Kirill-DoS/wasserschwein/hardware/cad/back_form_pusher.FCStd

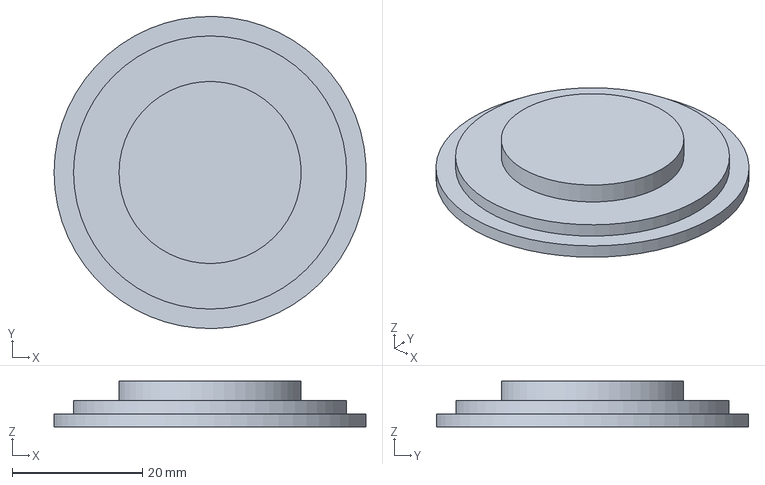
[picture p15: CAD file, 2026-05-06]
hardware/cad/back_form_pusher.FCStd
48.0 x 48.0 x 7.00 mm
