Kirill-DoS/wasserschwein/hardware/cad/NewPusherSys/ArmTightening.FCStd

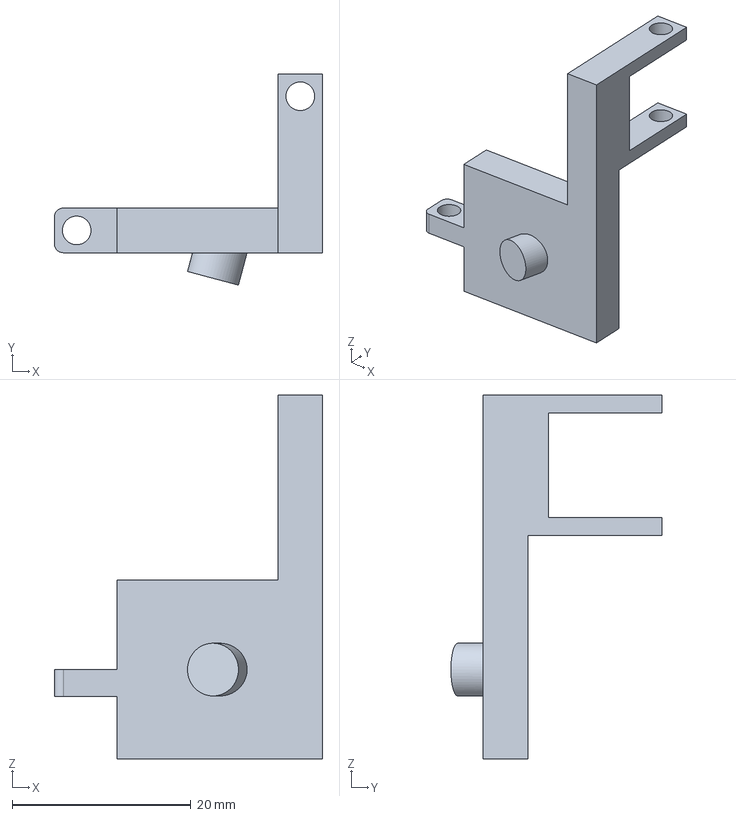
[picture p16: CAD file, 2026-05-06]
hardware/cad/NewPusherSys/ArmTightening.FCStd
30.0 x 23.6 x 40.7 mm
