Kirill-DoS/wasserschwein/hardware/cad/form_pusher.FCStd

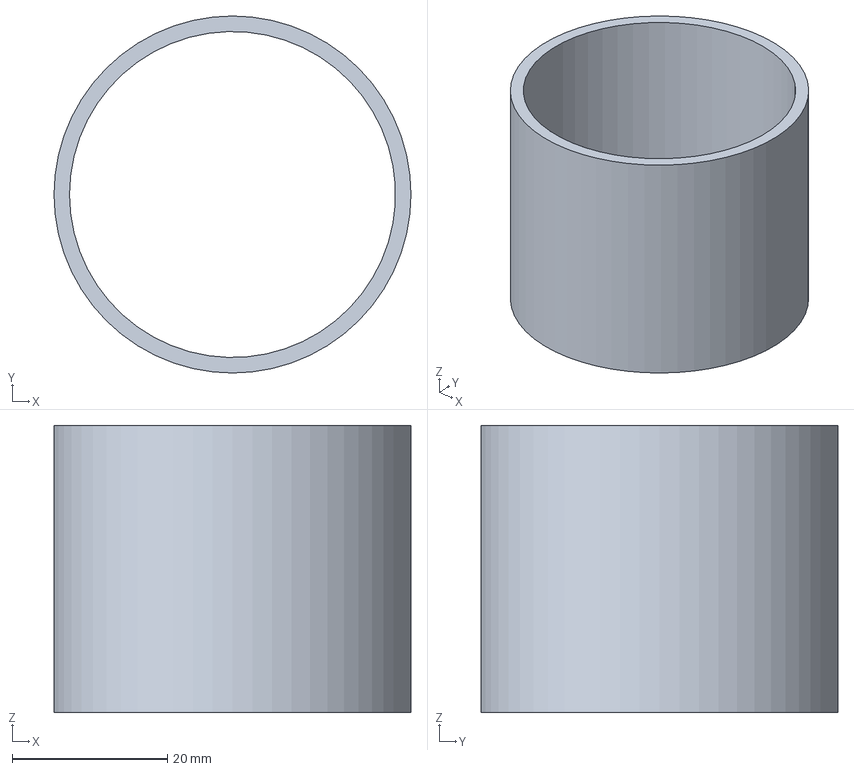
[picture p17: CAD file, 2026-05-06]
hardware/cad/form_pusher.FCStd
46.0 x 46.0 x 37.0 mm
