Kirill-DoS/wasserschwein/hardware/cad/NewPusherSys/BigGear.FCStd

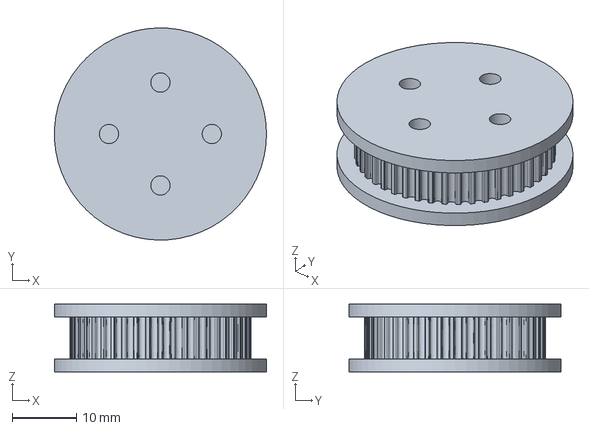
[picture p18: CAD file, 2026-05-06]
hardware/cad/NewPusherSys/BigGear.FCStd
33.0 x 33.0 x 10.5 mm
