Kirill-DoS/wasserschwein/hardware/cad/curtainDrive.FCStd

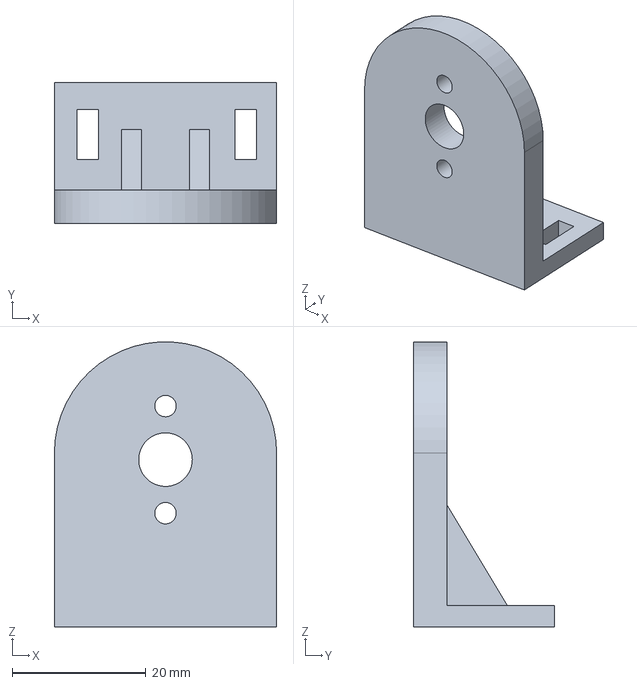
[picture p19: CAD file, 2026-05-06]
hardware/cad/curtainDrive.FCStd
33.2 x 21.0 x 42.6 mm
