Kirill-DoS/wasserschwein/hardware/cad/NewPusherSys/CurtainDrive.FCStd

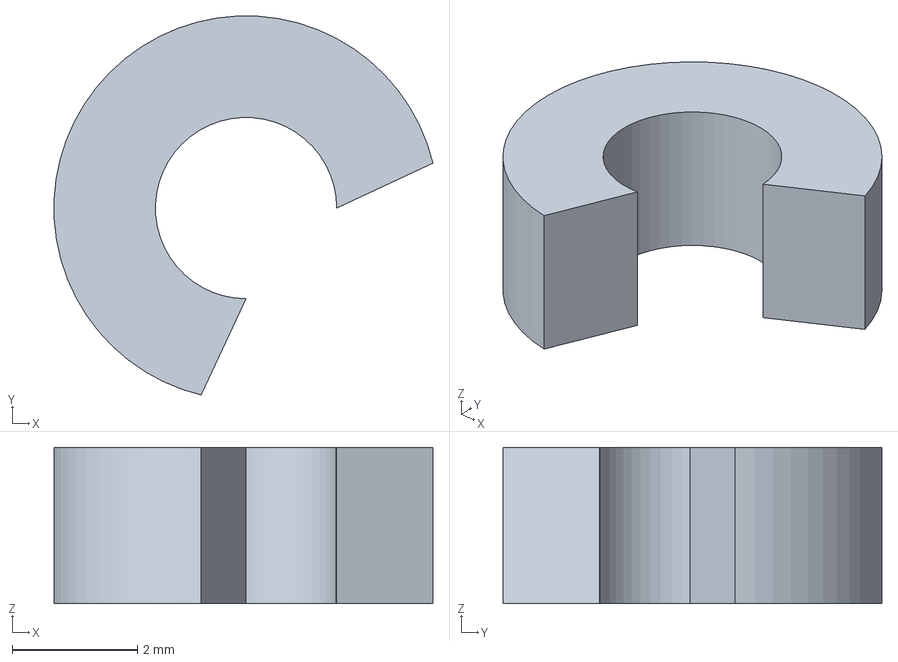
[picture p20: CAD file, 2026-05-06]
hardware/cad/NewPusherSys/CurtainDrive.FCStd
6.06 x 6.06 x 2.50 mm
