Kirill-DoS/wasserschwein/hardware/cad/NewPusherSys/WeelTightening.FCStd

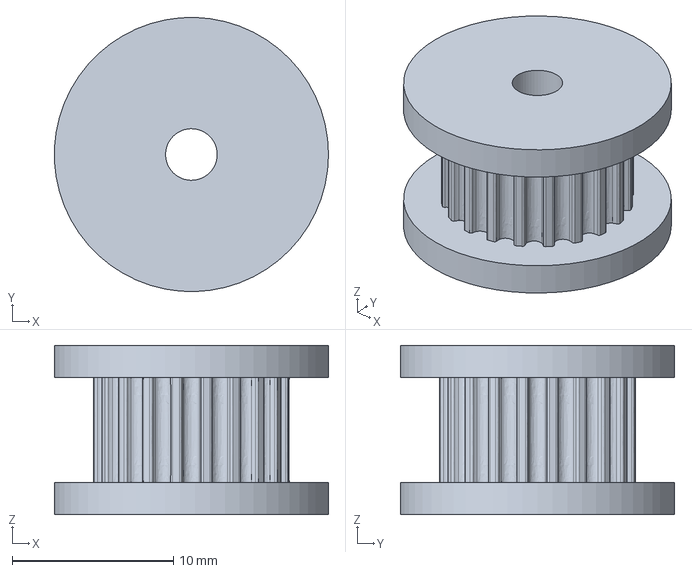
[picture p21: CAD file, 2026-05-06]
hardware/cad/NewPusherSys/WeelTightening.FCStd
17.0 x 17.0 x 10.5 mm
