Kirill-DoS/wasserschwein/hardware/cad/weel_involute_gear.FCStd

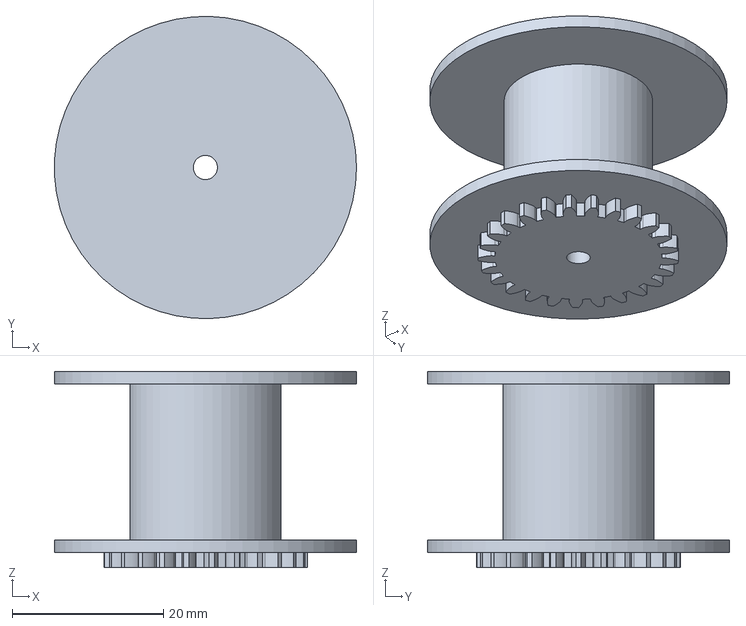
[picture p22: CAD file, 2026-03-06]
hardware/cad/weel_involute_gear.FCStd
40.0 x 40.0 x 26.0 mm
