Kirill-DoS/wasserschwein/hardware/cad/bevel_gear_3.FCStd

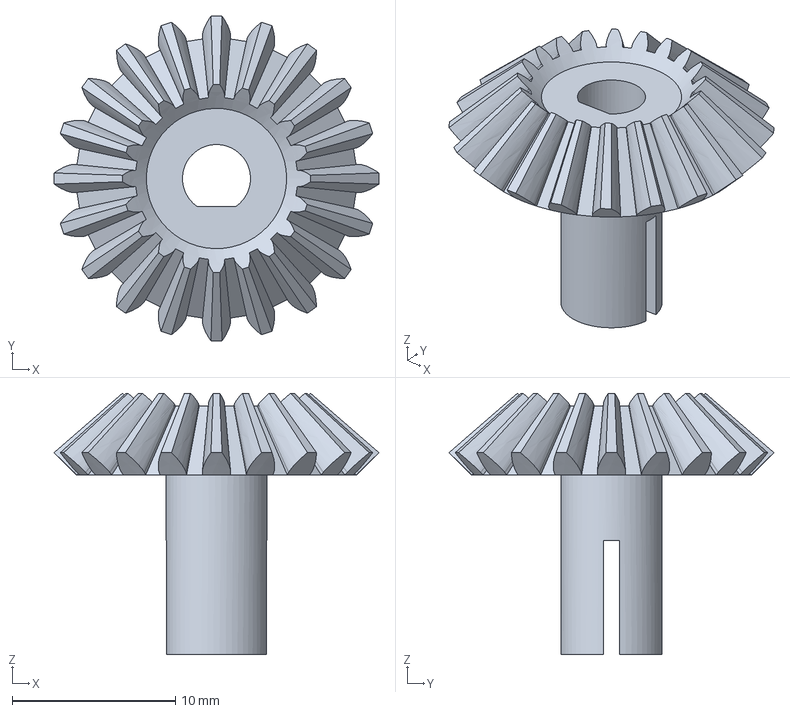
[picture p23: CAD file, 2026-03-06]
hardware/cad/bevel_gear_3.FCStd
19.9 x 19.9 x 16.0 mm
