Kirill-DoS/wasserschwein/hardware/cad/BLCD_kipper.FCStd

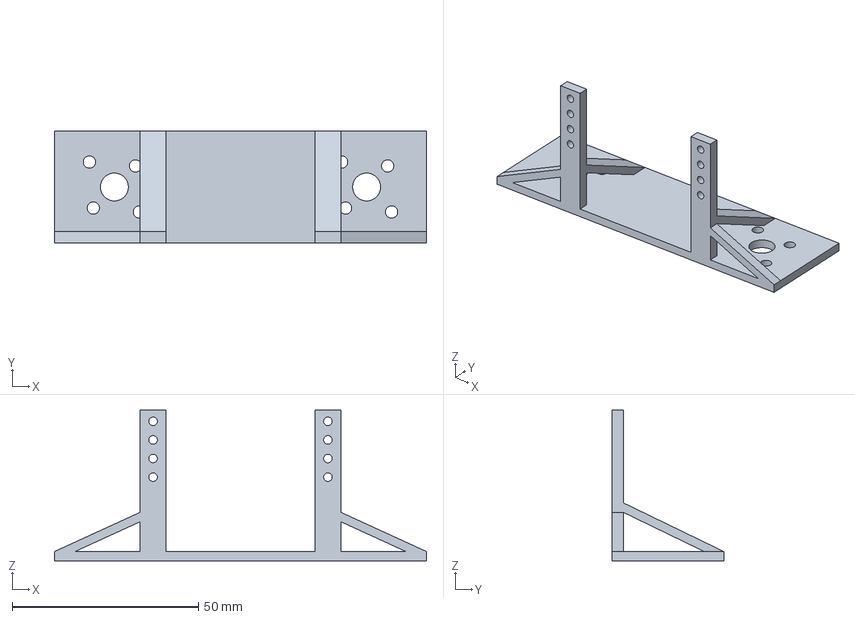
[picture p24: CAD file, 2026-03-06]
hardware/cad/BLCD_kipper.FCStd
100.0 x 30.0 x 40.5 mm
