Kirill-DoS/wasserschwein/hardware/cad/arcanoid_new.FCStd

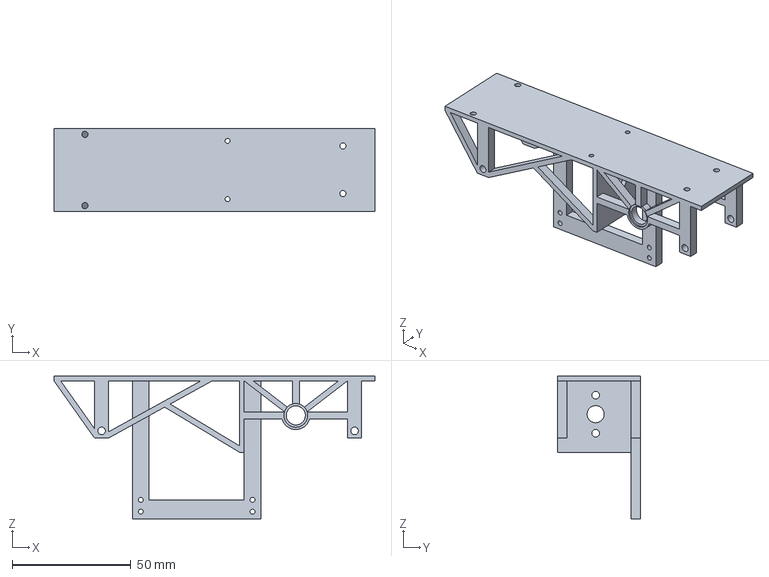
[picture p25: CAD file, 2026-03-06]
hardware/cad/arcanoid_new.FCStd
135.0 x 34.8 x 60.0 mm
