Kirill-DoS/wasserschwein/hardware/cad/brain_kipper.FCStd

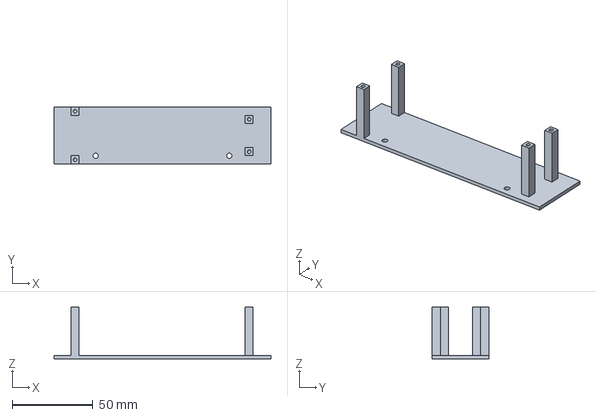
[picture p26: CAD file, 2026-03-06]
hardware/cad/brain_kipper.FCStd
134.0 x 35.0 x 32.0 mm
