Kirill-DoS/wasserschwein/hardware/cad/board_stands.3mf

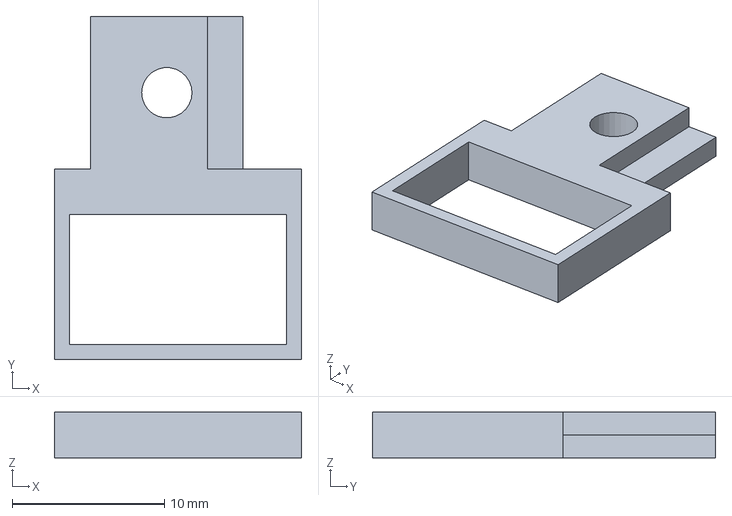
[picture p27: CAD file, 2026-03-06]
hardware/cad/board_stands.3mf
16.2 x 22.5 x 3.00 mm
