Kirill-DoS/wasserschwein/hardware/cad/lateral_weel.FCStd

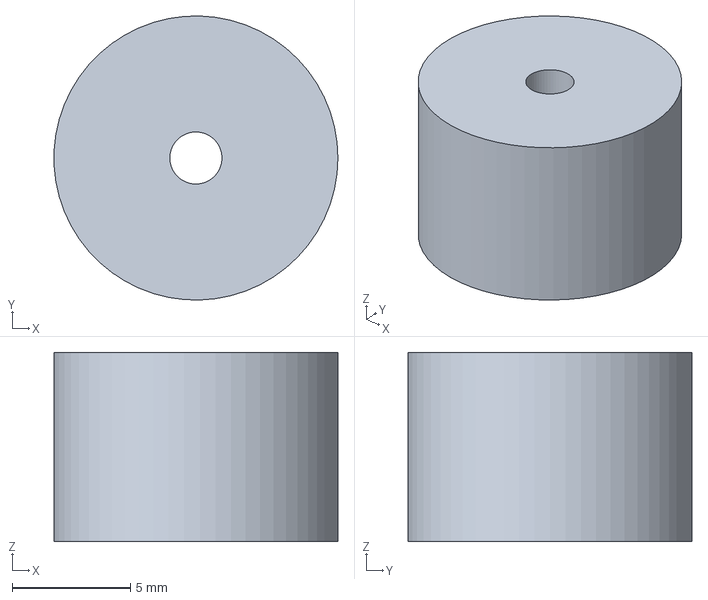
[picture p28: CAD file, 2026-01-27]
hardware/cad/lateral_weel.FCStd
12.0 x 12.0 x 8.00 mm
