Kirill-DoS/wasserschwein/hardware/cad/arcanoid1.3mf.FCStd

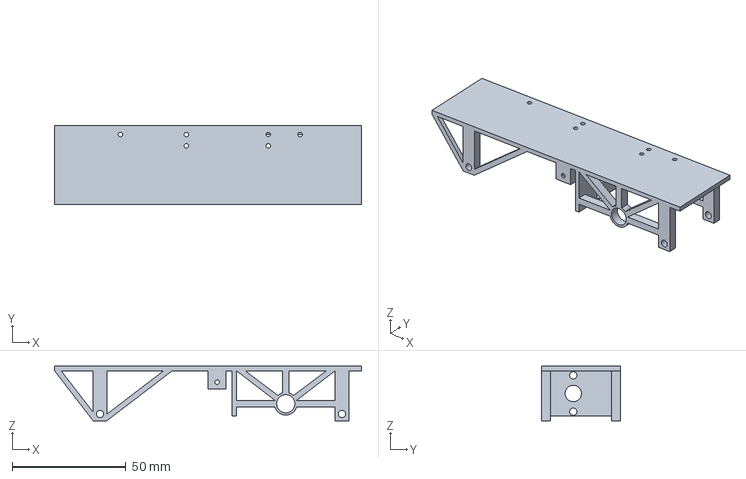
[picture p29: CAD file, 2026-01-27]
hardware/cad/arcanoid1.3mf.FCStd
135.0 x 34.8 x 24.0 mm
