Kirill-DoS/wasserschwein/hardware/cad/bevel_gear_1.FCStd

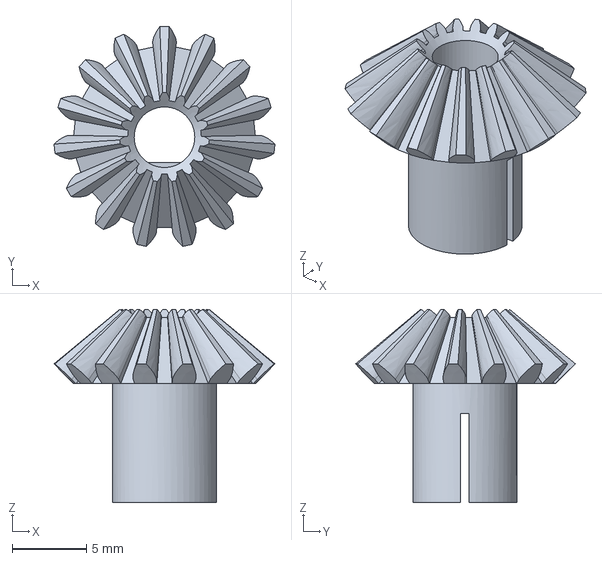
[picture p30: CAD file, 2026-01-27]
hardware/cad/bevel_gear_1.FCStd
14.9 x 14.8 x 13.0 mm
