Kirill-DoS/wasserschwein/hardware/cad/lateral support.FCStd

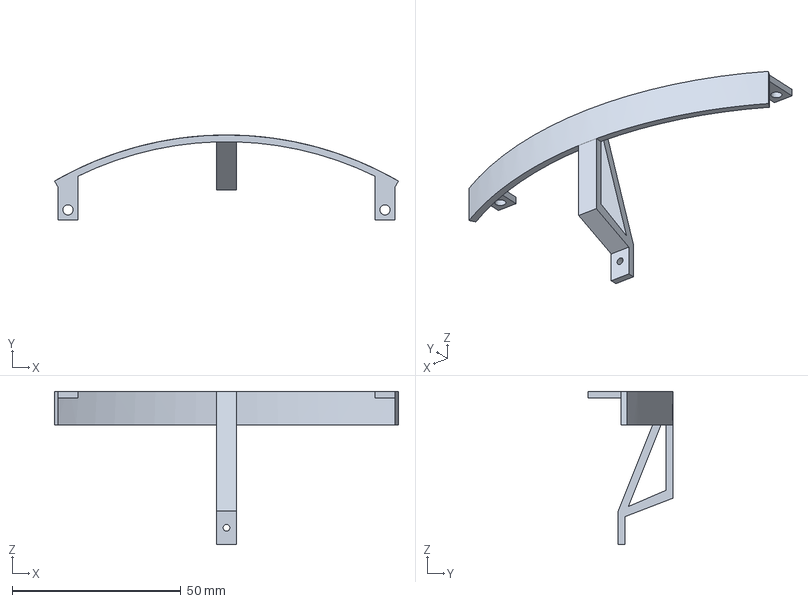
[picture p31: CAD file, 2026-01-27]
hardware/cad/lateral support.FCStd
102.0 x 25.2 x 45.5 mm
